R-Mutura/calve_heater/hardware/ASSETS/IMG_20220107_123302.jpg

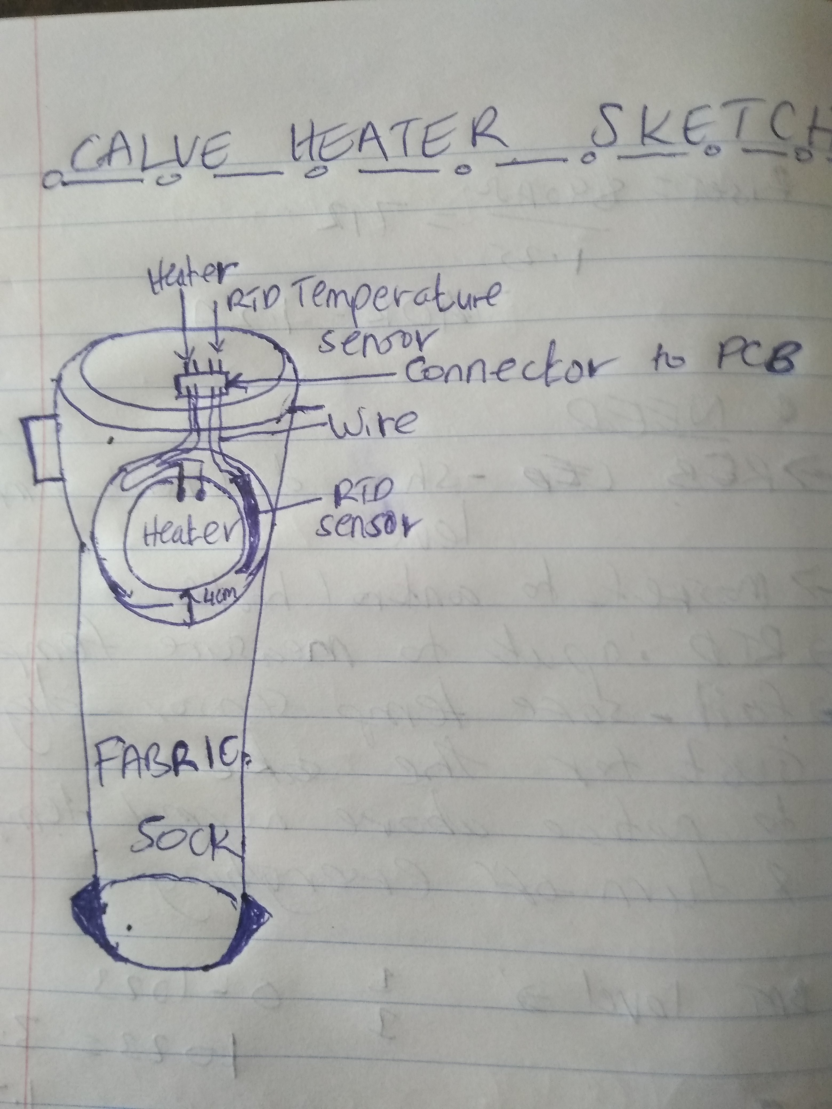
hardware/ASSETS/IMG_20220107_123302.jpg
